gert-lauritsen/Loftrel-Round/PCB/Simulation/ZeroDetect.asc

C1: cap; 2µ2
D1: diode
D2: diode
R1: res; 200k
R2: res; 100k
R3: res; 1000k
R4: res; 100k
U1: PC817A
V1: voltage; SINE(0 230 50 0 0 0 10)
V2: voltage; 3.3
Named nets: 0
.tran 1000m
