gert-lauritsen/Loftrel-Round/ACMonitorHA_Web/secrets.h

// secrets.h
#pragma once

#define sWIFI_SSID     "askob"
#define sWIFI_PASS     "bingeling"
#define sMQTT_SERVER   "10.160.0.156"
#define sMQTT_USER     ""
#define sMQTT_PASS     ""

// Static IP configuration
#define LOCAL_IP      10,160,0,210
#define GATEWAY_IP    10,160,0,1
#define SUBNET_MASK   255,255,255,0
